luispichio/Telnet4DosFBB/images/foto1.jpg

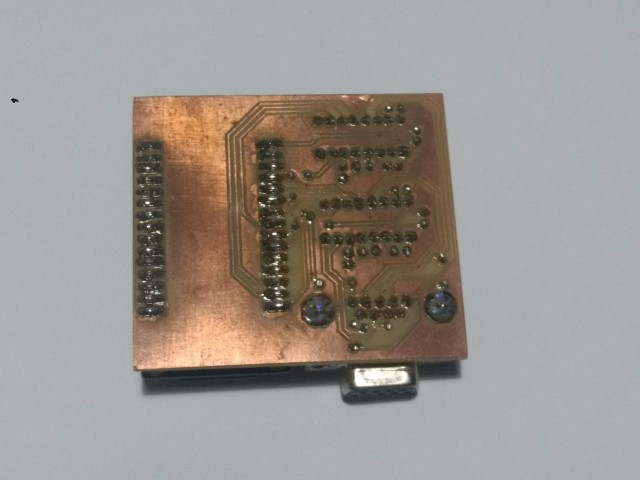
images/foto1.jpg
