luispichio/Telnet4DosFBB/images/foto2.jpg

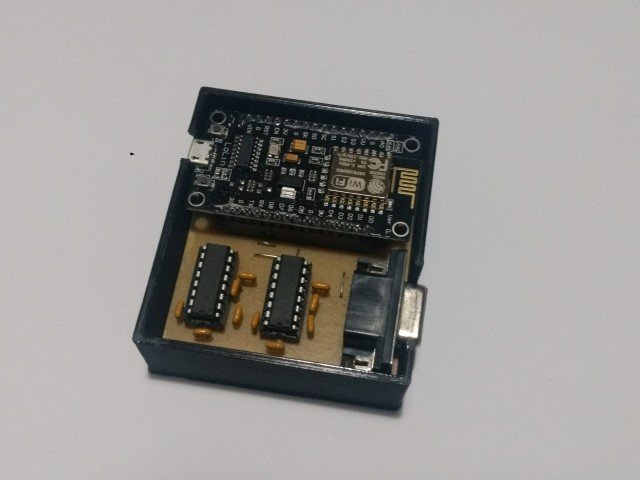
images/foto2.jpg
